vingarzan/star-trek-display/outputs/corner_braced_arm_preview.png

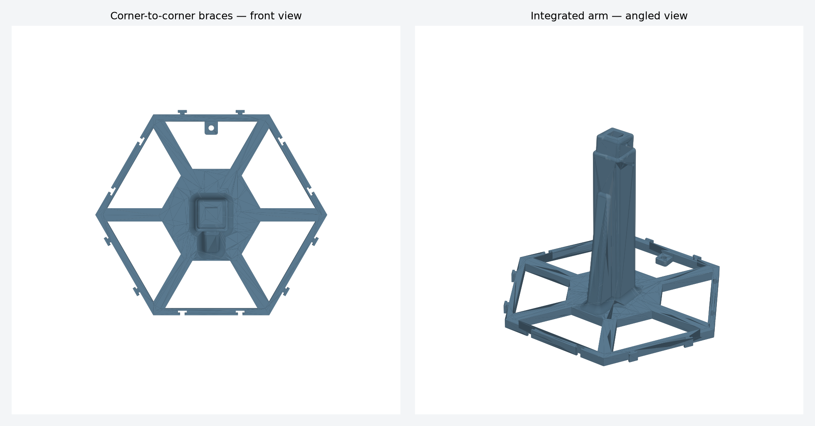
outputs/corner_braced_arm_preview.png
