vingarzan/star-trek-display/outputs/empty_hex_preview.png

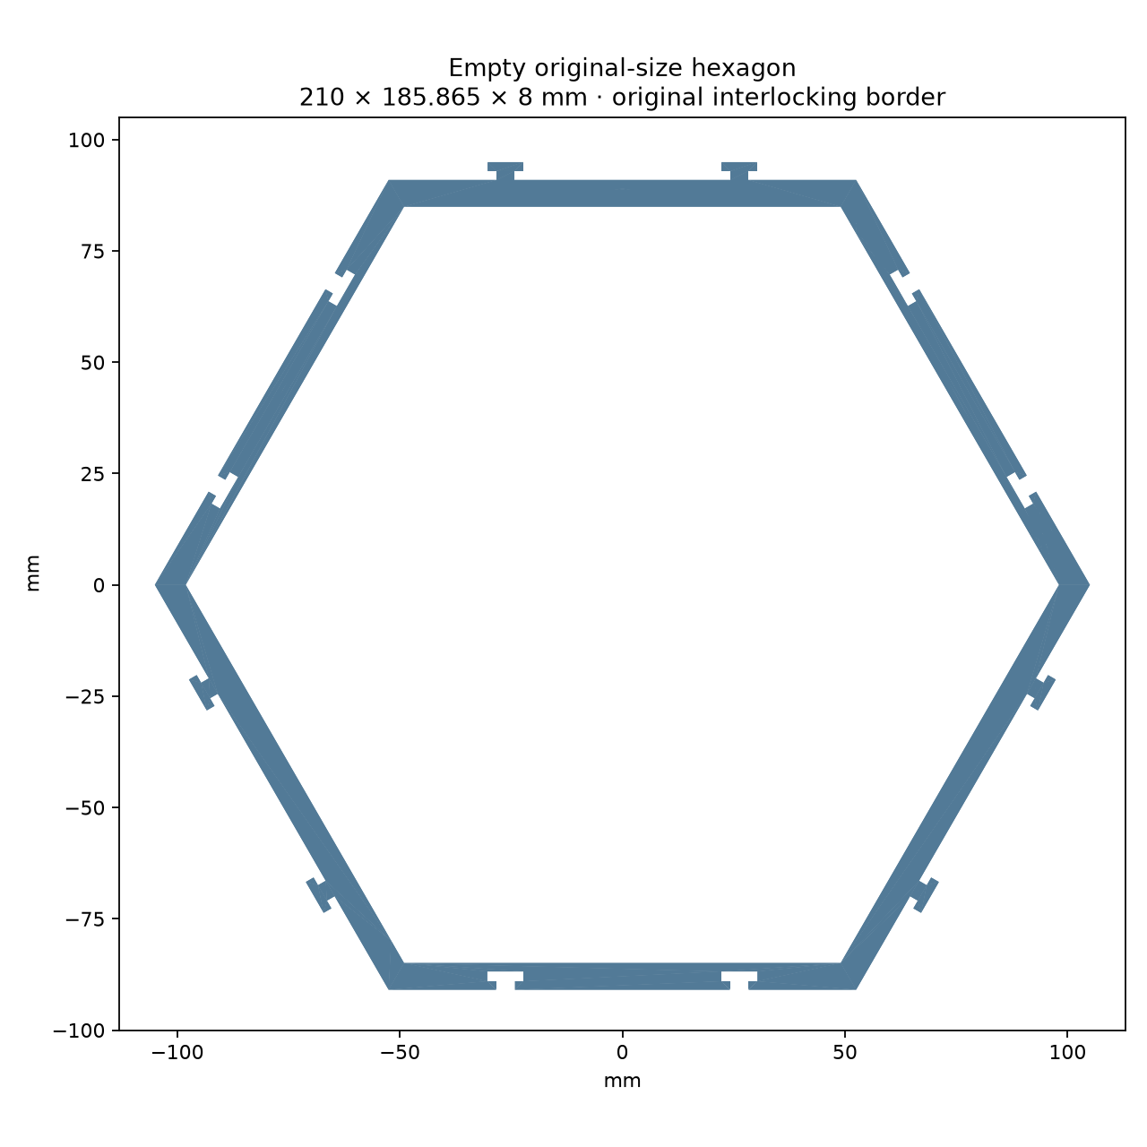
outputs/empty_hex_preview.png
