vingarzan/star-trek-display/outputs/filled_title_notch_preview.png

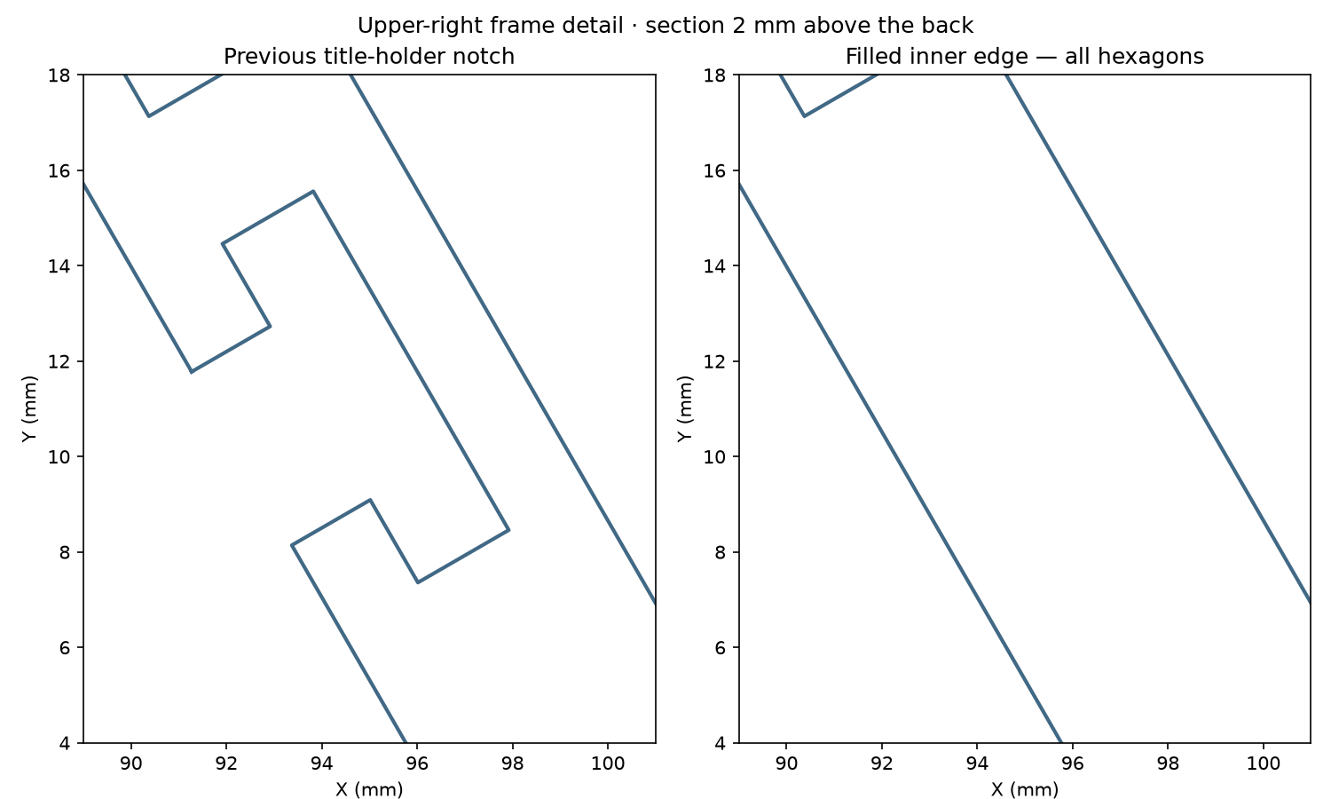
outputs/filled_title_notch_preview.png
