vingarzan/star-trek-display/outputs/galaxy_holder_preview.png

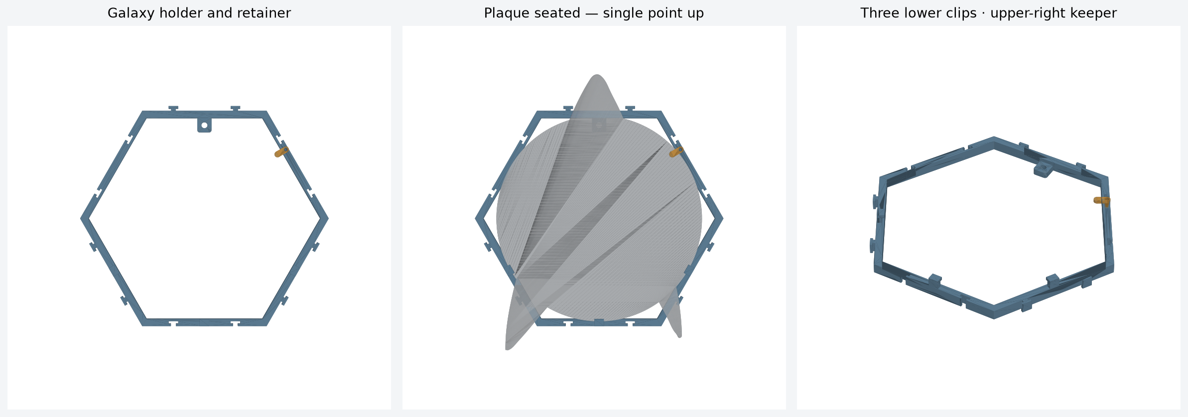
outputs/galaxy_holder_preview.png
