vingarzan/star-trek-display/outputs/nail_cover_preview.png

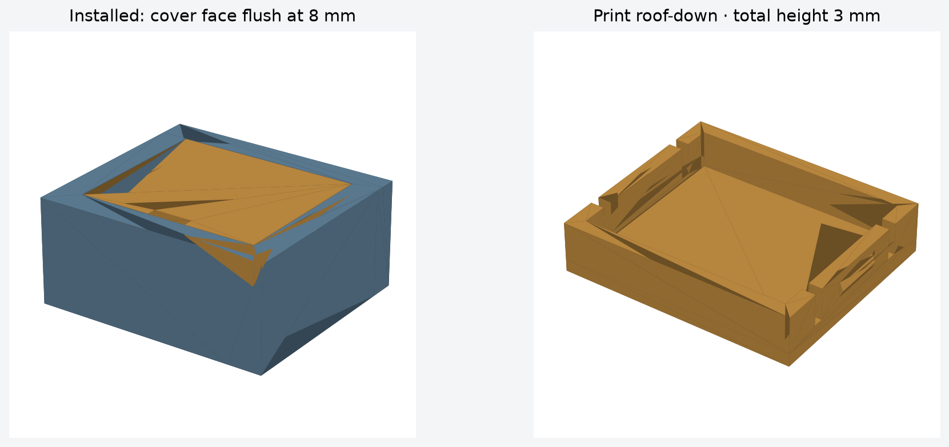
outputs/nail_cover_preview.png
