vingarzan/star-trek-display/outputs/peg_5mm_preview.png

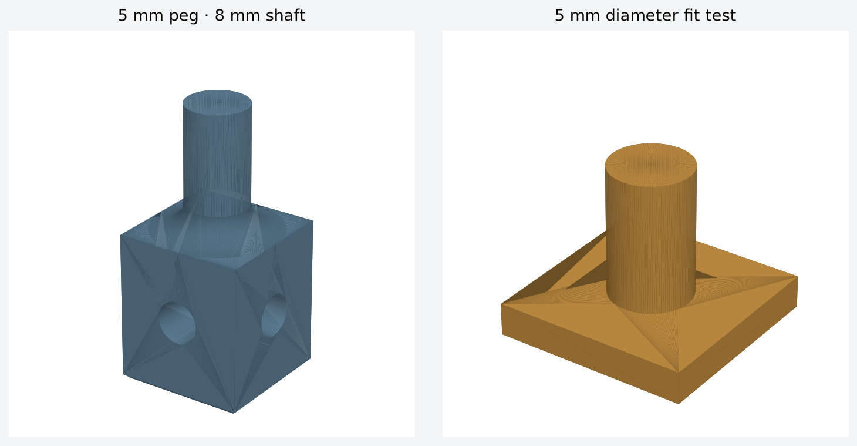
outputs/peg_5mm_preview.png
