vingarzan/star-trek-display/outputs/snug_stems_preview.png

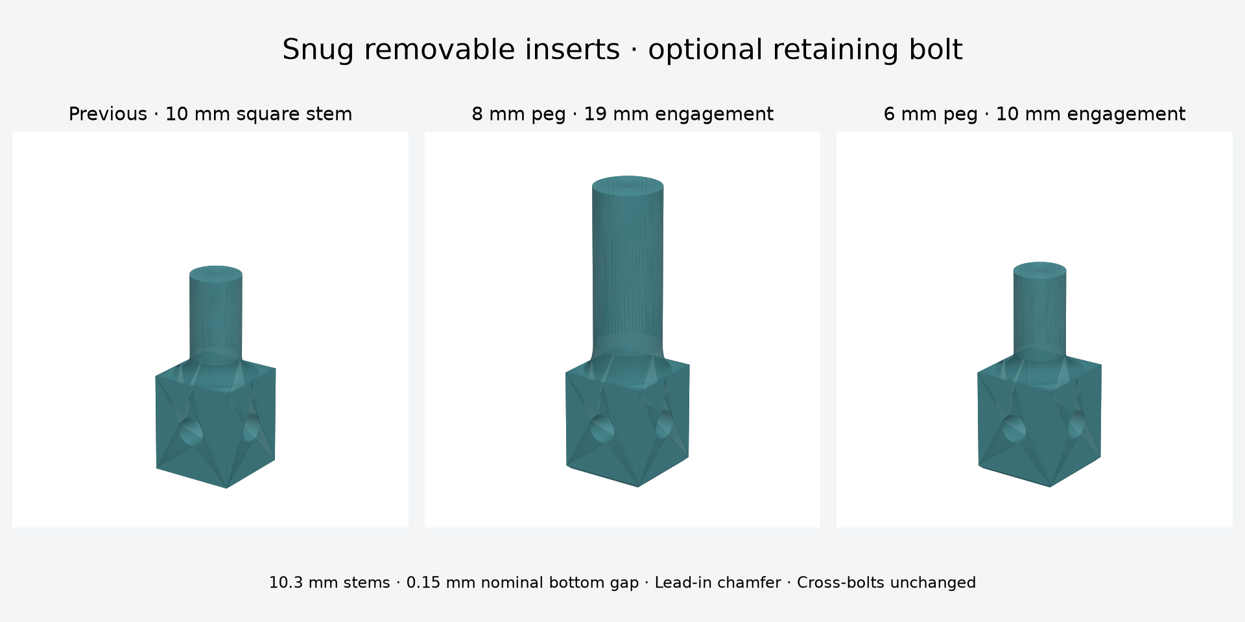
outputs/snug_stems_preview.png
