vingarzan/star-trek-display/outputs/hex_plaque_snug_5.7mm.stl

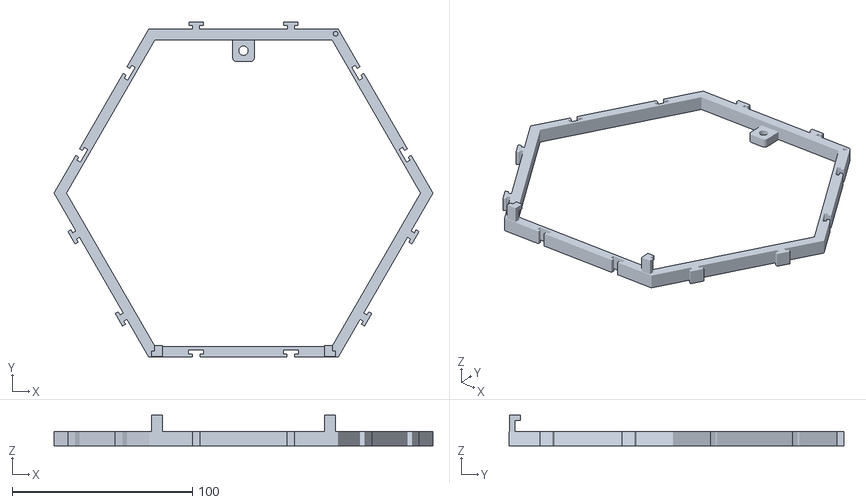
[picture p22: CAD file, 2026-10-04]
outputs/hex_plaque_snug_5.7mm.stl
210.0 x 185.9 x 16.9
