vingarzan/star-trek-display/outputs/fit_test_arm_stem_10.3mm.stl

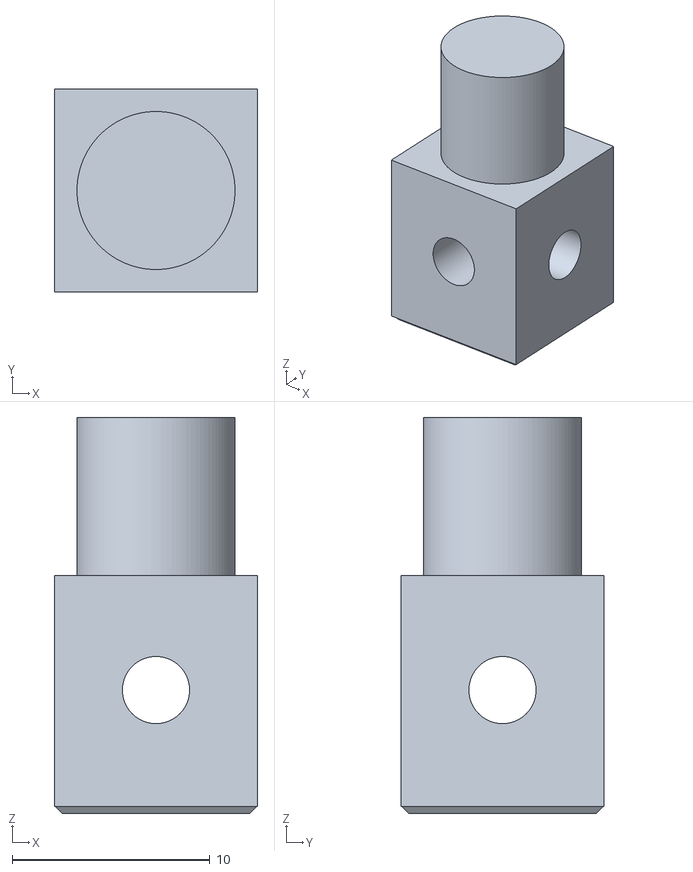
[picture p23: CAD file, 2026-10-04]
outputs/fit_test_arm_stem_10.3mm.stl
10.3 x 10.3 x 20.0
