vingarzan/star-trek-display/outputs/peg_insert_8mm.stl

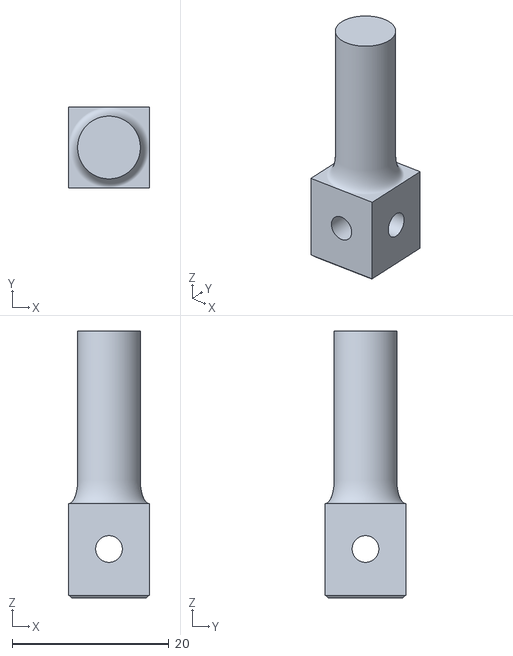
[picture p24: CAD file, 2026-10-04]
outputs/peg_insert_8mm.stl
10.3 x 10.3 x 34.0
