vingarzan/star-trek-display/outputs/peg_insert_6mm.stl

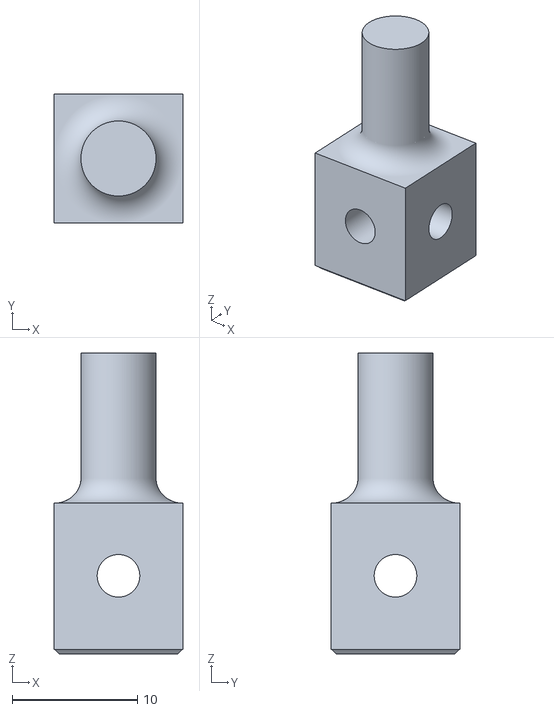
[picture p25: CAD file, 2026-10-04]
outputs/peg_insert_6mm.stl
10.3 x 10.3 x 24.0
