vingarzan/star-trek-display/outputs/fit_test_peg_6.0mm.stl

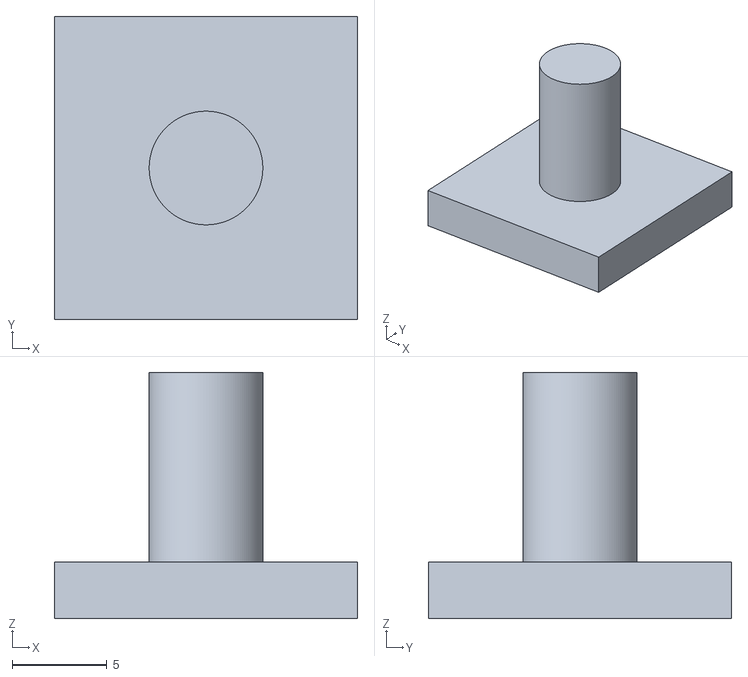
[picture p26: CAD file, 2026-10-04]
outputs/fit_test_peg_6.0mm.stl
16.0 x 16.0 x 13.0
