vingarzan/star-trek-display/outputs/fit_test_plate_gap_5.7mm.stl

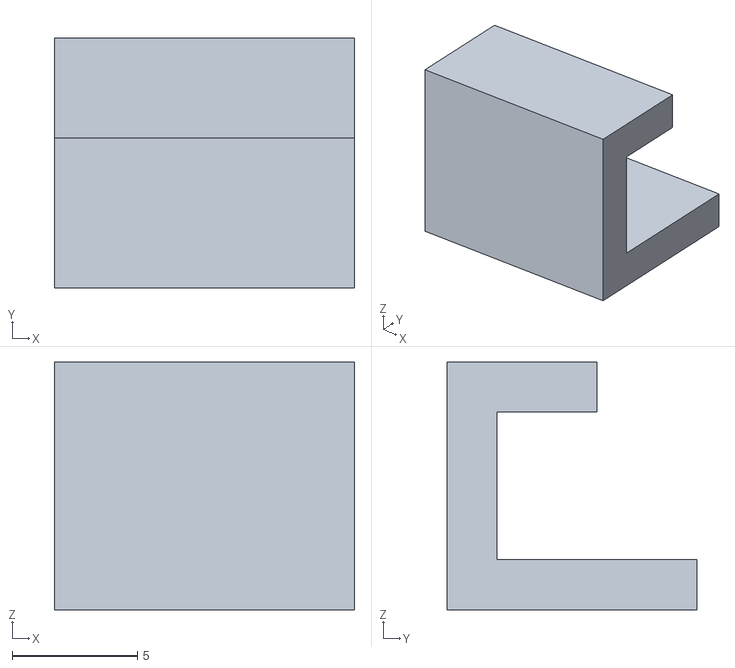
[picture p27: CAD file, 2026-10-04]
outputs/fit_test_plate_gap_5.7mm.stl
12.0 x 10.0 x 9.90
