vingarzan/star-trek-display/outputs/plaque_latch_snug_5.7mm.stl

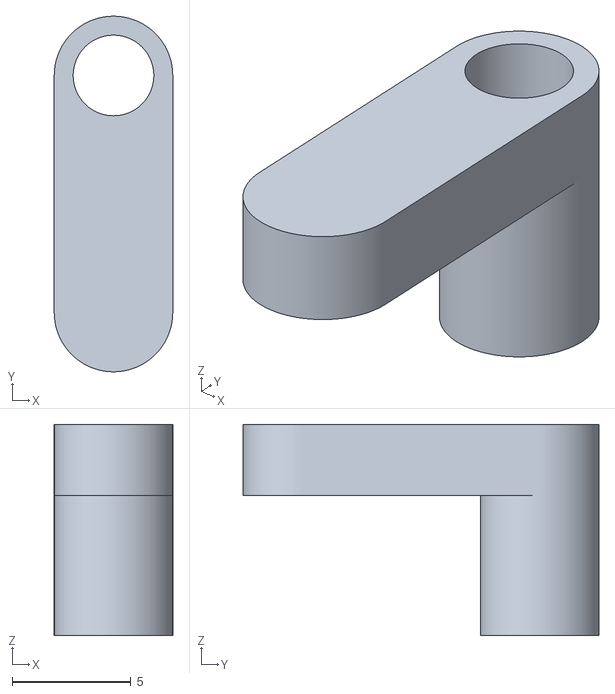
[picture p30: CAD file, 2026-10-04]
outputs/plaque_latch_snug_5.7mm.stl
5.00 x 15.0 x 8.90
