vingarzan/star-trek-display/outputs/fit_test_peg_8.0mm.stl

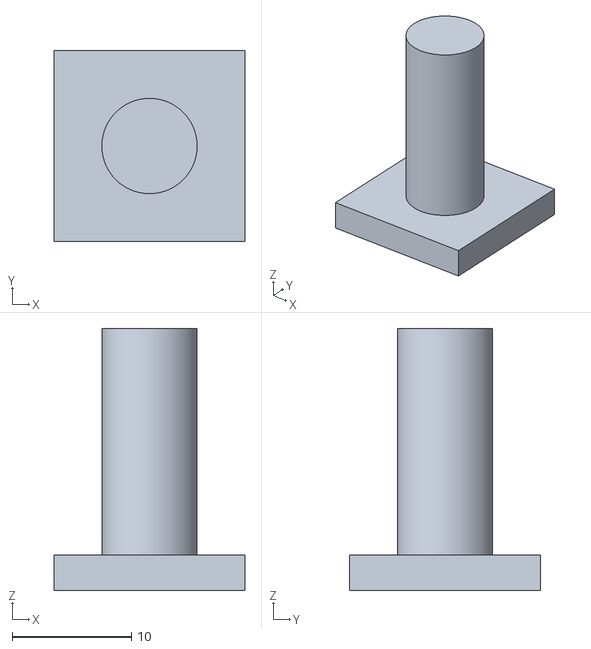
[picture p31: CAD file, 2026-10-04]
outputs/fit_test_peg_8.0mm.stl
16.0 x 16.0 x 22.0
