vingarzan/star-trek-display/outputs/fit_test_peg_7.8mm.stl

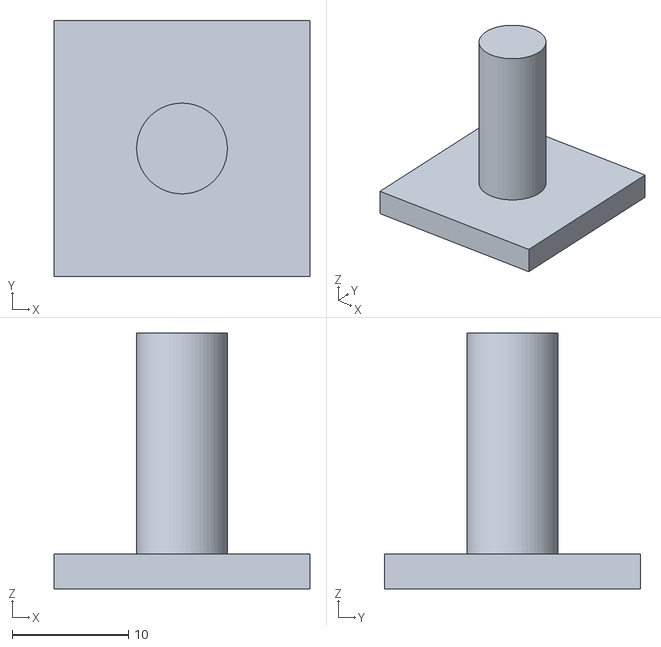
[picture p32: CAD file, 2026-10-04]
outputs/fit_test_peg_7.8mm.stl
22.0 x 22.0 x 22.0
