vingarzan/star-trek-display/outputs/fit_test_original_joint_bottom.stl

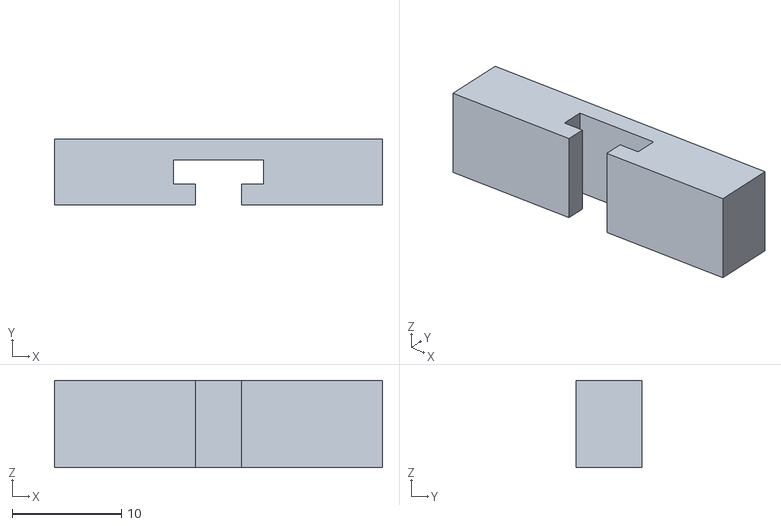
[picture p33: CAD file, 2026-10-04]
outputs/fit_test_original_joint_bottom.stl
30.0 x 6.00 x 8.00
