vingarzan/star-trek-display/outputs/fit_test_socket.stl

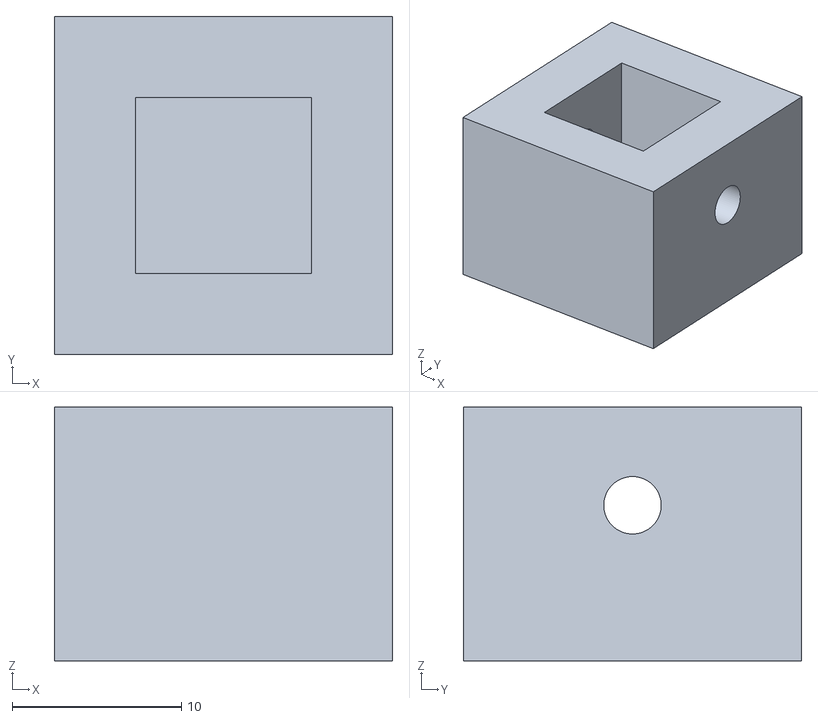
[picture p34: CAD file, 2026-10-04]
outputs/fit_test_socket.stl
20.0 x 20.0 x 15.0
