vingarzan/star-trek-display/outputs/fit_test_original_joint_top.stl

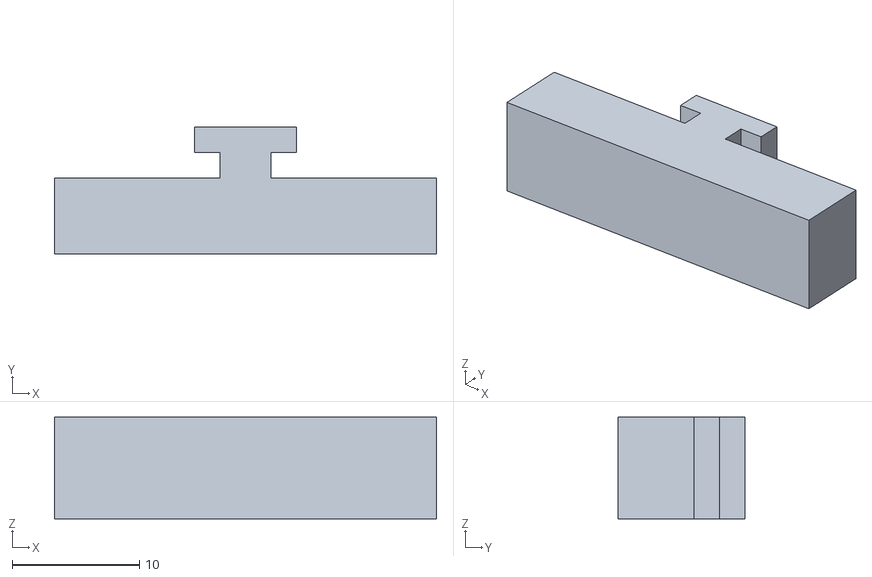
[picture p35: CAD file, 2026-10-04]
outputs/fit_test_original_joint_top.stl
30.0 x 10.0 x 8.00
